paul-lebel/magic-music-box/magicbox/ui/constants.py

# Constants for magic_box and magic_box_screen



# Main interface buttons
BTN_A = 17
BTN_B = 27
BTN_C = 0
BTN_D = 5
BTN_E = 6
