paul-lebel/magic-music-box/magicbox/tft_examples/sia-clock-tft.py

#!/usr/bin/env python3
# -*- coding: utf-8 -*-

import glob
import os
import time
import json
from sys import exit
import requests

from font_fredoka_one import FredokaOne
from PIL import Image, ImageDraw, ImageFont

import geocoder
import digitalio
import board

from adafruit_rgb_display.rgb import color565
from adafruit_rgb_display import st7789


# Get the current path
PATH = os.path.dirname(__file__)

# Details to customise the weather display
CITY = "Redwood City"
COUNTRYCODE = "US"
WEEKDAYS = ["Monday", "Tuesday", "Wednesday", "Thursday", "Friday"]
BAUDRATE = 64000000  # The pi can be very fast!
DT_UPDATE_WEATHER = 60
DT_UPDATE_TIME = 1
RED = (255, 0, 0)
WHITE = (255,255,255)
ORANGE = (255, 165, 0)
BLUE = (0,0,255)

CLOCK_FONT = ImageFont.truetype(FredokaOne, 50)
FONT = ImageFont.truetype(FredokaOne, 25)


class Display(st7789.ST7789):
# Subclass to wrap buttons and backlight into same object

    def __init__(self):

        # Configuration for CS and DC pins for Raspberry Pi
        cs_pin = digitalio.DigitalInOut(board.CE0)
        dc_pin = digitalio.DigitalInOut(board.D25)
        reset_pin = None

        super().__init__(
        board.SPI(),
        cs=cs_pin,
        dc=dc_pin,
        rst=reset_pin,
        baudrate=BAUDRATE,
        width=240,
        height=240,
        x_offset=0,
        y_offset=80,
        )

        self.backlight = digitalio.DigitalInOut(board.D22)
        self.backlight.switch_to_output()
        self.backlight.value = True
        self.buttonA = digitalio.DigitalInOut(board.D23)
        self.buttonB = digitalio.DigitalInOut(board.D24)
        self.buttonA.switch_to_input()
        self.buttonB.switch_to_input()
        self.buttonA.pull = digitalio.Pull.UP
        self.buttonB.pull = digitalio.Pull.UP


# Convert a city name and country code to latitude and longitude
def get_coords(address):
    g = geocoder.arcgis(address)
    coords = g.latlng
    return coords


# Query OpenMeteo (https://open-meteo.com) to get current weather data
def get_weather(address):
    coords = get_coords(address)
    weather = {}
    res = requests.get("https://api.open-meteo.com/v1/forecast?latitude=" + str(coords[0]) + "&longitude=" + str(coords[1]) + "&current_weather=true")
    if res.status_code == 200:
        j = json.loads(res.text)
        current = j["current_weather"]
        weather["temperature"] = current["temperature"]
        weather["windspeed"] = current["windspeed"]
        weather["weathercode"] = current["weathercode"]
        return weather
    else:
        return weather

def C_to_F(temp_C):
    return -40 + (temp_C + 40)*1.8 

def kmh_to_mph(speed_kmh):
    return speed_kmh/1.6
    

def main():

    display = Display()

    location_string = "{city}, {countrycode}".format(city=CITY, countrycode=COUNTRYCODE)

    # Turn on backlight
    display.backlight.value = True

    # Dictionaries to store our icons and icon masks in
    icons = {}
    masks = {}
    weather = None

    # This maps the weather code from Open Meteo
    # to the appropriate weather icons
    # Weather codes from https://open-meteo.com/en/docs
    icon_map = {
        "snow": [71, 73, 75, 77, 85, 86],
        "rain": [51, 53, 55, 56, 57, 61, 63, 65, 66, 67, 80, 81, 82],
        "cloud": [1, 2, 3, 45, 48],
        "sun": [0],
        "storm": [95, 96, 99],
        "wind": []
    } 

    t_weather = -DT_UPDATE_WEATHER
    t_time = -DT_UPDATE_TIME
    prev_btnA_value = 1

    try: 
        while True:

            # Toggle backlight only if it's a falling edge
            btnA_value = display.buttonA.value

            if prev_btnA_value and (not btnA_value):
                if display.backlight.value:
                    display.backlight.value = 0
                elif display.backlight.value == 0:
                    display.backlight.value = 1

            prev_btnA_value = btnA_value


            # Get the weather data for the given location
            if (time.perf_counter() - t_weather) > DT_UPDATE_WEATHER:
                print("Time to check the weather...")
                try:
                    weather = get_weather(location_string)
                    t_weather = time.perf_counter()
                except:
                    pass

                if weather:
                    temperature = C_to_F(weather["temperature"])
                    windspeed = kmh_to_mph(weather["windspeed"])
                    weathercode = weather["weathercode"]

                    for icon in icon_map:
                        if weathercode in icon_map[icon]:
                            weather_icon = icon
                            break

                    # Load our icon files and generate masks
                    for icon in glob.glob(os.path.join(PATH, "images/icon-*.png")):
                        icon_name = icon.split("icon-")[1].replace(".png", "")
                        icon_image = Image.open(icon)
                        icons[icon_name] = icon_image
                        # Don't need masks with RGB color display
                        # masks[icon_name] = create_mask(icon_image)
                
                else:
                    windspeed = 0.0
                    temperature = 0.0
                    weather_icon = None

            if (time.perf_counter() - t_time) > DT_UPDATE_TIME:

                # Create a new canvas to draw on
                image = Image.new('RGB', (display.width, display.height))
                draw = ImageDraw.Draw(image)
                draw.rectangle((0, 0, display.width, display.height), outline=0, fill=(0, 0, 0))
                # display.image(image)

                # Write text with weather values to the canvas
                date = time.strftime("%m/%d")
                time_for_clock = time.strftime("%-I:%M %p")
                hour = int(time.strftime("%H"))
                minute = int(time.strftime("%M"))
                day = time.strftime("%A")

                time_decimal = (hour + minute/60)

                if day in WEEKDAYS:
                    print("It's a weekday!")
                    if (time_decimal < 6.75) or (time_decimal > 19.75):
                        time_color = RED
                    elif time_decimal >= 19.25:
                        time_color = ORANGE
                    else:
                        time_color = WHITE

                else:
                    print("It's the weekend!")
                    if (time_decimal < 7) or (time_decimal > 20):
                        time_color = RED
                    elif time_decimal >= 19.5:
                        time_color = ORANGE
                    else:
                        time_color = WHITE

                if temperature > 85:
                    temperature_color = (255, 0, 0)
                elif temperature < 40:
                    temperature_color = (0, 0, 255)
                else:
                    temperature_color = (255, 255, 255)

                print(time_color)
                draw.text((0, 25), time_for_clock, time_color, font=CLOCK_FONT)
                draw.text((0, 120), "Date: " + date, (255, 255, 255), font=FONT)
                draw.text((0, 150), "Temp: {0:.1f}°F".format(temperature), temperature_color, font=FONT)
                draw.text((0, 180), "Wind: {0:.1f}mph".format(windspeed), (255,255,255), font=FONT)

                # Draw the current weather icon over the backdrop
                if weather_icon is not None:
                    image.paste(icons[weather_icon], (165, 130))

                display.image(image, 180)
                t_time = time.perf_counter()


    except KeyboardInterrupt:
        pass
  

if __name__ == "__main__":
    main()
